doughnut923/Blossom/Renders/new_smoke.png

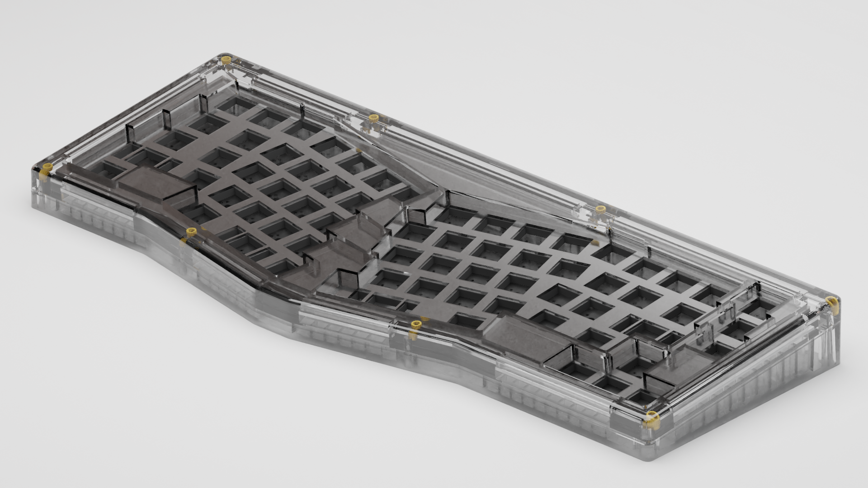
Renders/new_smoke.png
